ThingPulse/esp32-cubo/data/Bonjour_01.png

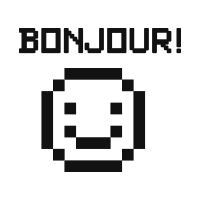
data/Bonjour_01.png
