ThingPulse/esp32-cubo/data/Bonjour_02.png

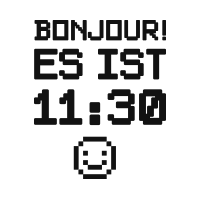
data/Bonjour_02.png
