ThingPulse/esp32-cubo/data/Cubo_DPS_01.jpg

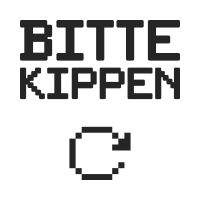
data/Cubo_DPS_01.jpg
