ThingPulse/esp32-cubo/data/Cubo_DPS_02.jpg

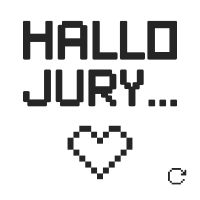
data/Cubo_DPS_02.jpg
