ThingPulse/esp32-cubo/data/Cubo_DPS_03.jpg

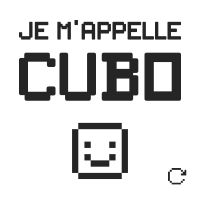
data/Cubo_DPS_03.jpg
