ThingPulse/esp32-cubo/data/Cubo_DPS_04.jpg

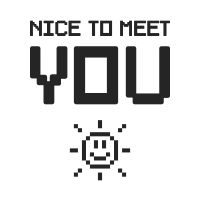
data/Cubo_DPS_04.jpg
