ThingPulse/esp32-cubo/data/Cubo_DPS_05.jpg

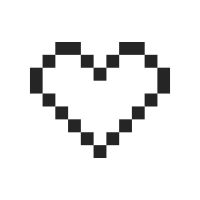
data/Cubo_DPS_05.jpg
