ThingPulse/esp32-cubo/data/Cubo_DPS_06.jpg

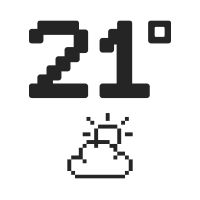
data/Cubo_DPS_06.jpg
