ThingPulse/esp32-cubo/data/Date.png

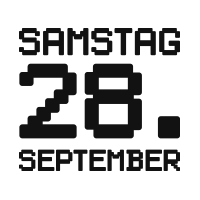
data/Date.png
