ThingPulse/esp32-cubo/data/Heart.png

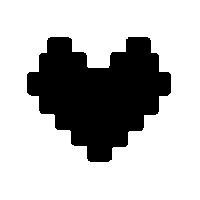
data/Heart.png
