ThingPulse/esp32-cubo/data/kippen.png

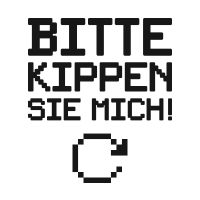
data/kippen.png
