ThingPulse/esp32-cubo/data/Spruch.png

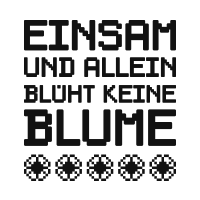
data/Spruch.png
