ThingPulse/esp32-cubo/data/Spruch_01.png

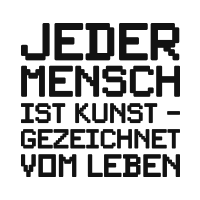
data/Spruch_01.png
