ThingPulse/esp32-cubo/data/Spruch_02.png

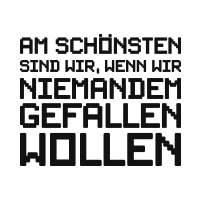
data/Spruch_02.png
