ThingPulse/esp32-cubo/data/Weather_new.png

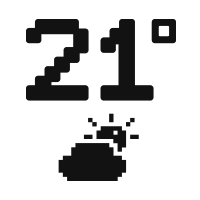
data/Weather_new.png
