ThingPulse/esp32-cubo/data/willkommen_hack.png

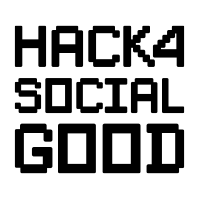
data/willkommen_hack.png
